mdouchement/Ampeg-Heritage-B-15/Documents/_2011 Heritage HB15.jpg

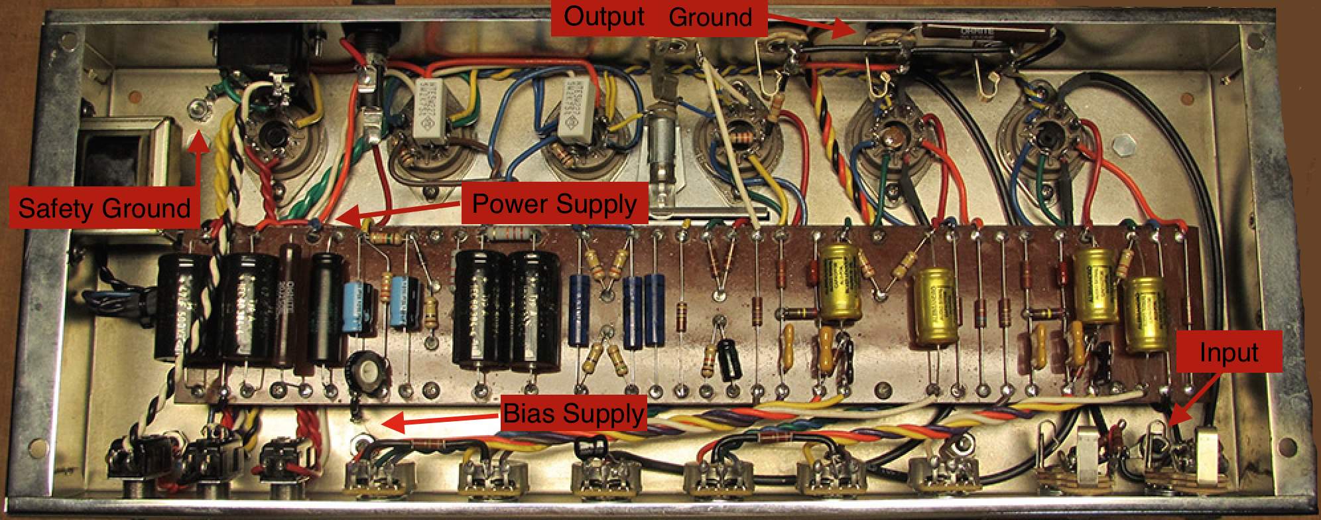
Documents/_2011 Heritage HB15.jpg
