mdouchement/Ampeg-Heritage-B-15/Measures/1964.mods.png

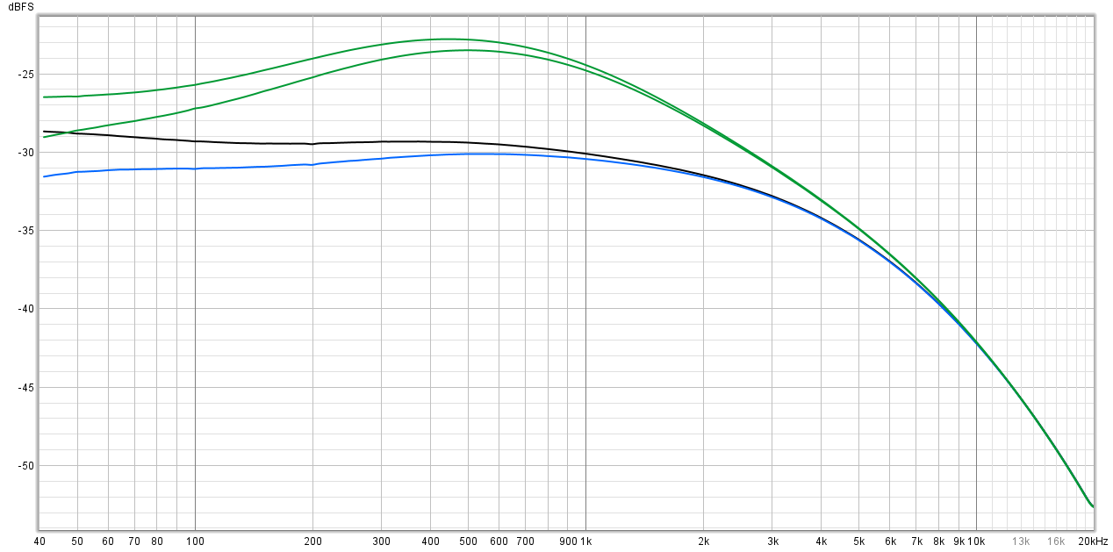
Measures/1964.mods.png
