mdouchement/Ampeg-Heritage-B-15/Measures/1964.tonestack.png

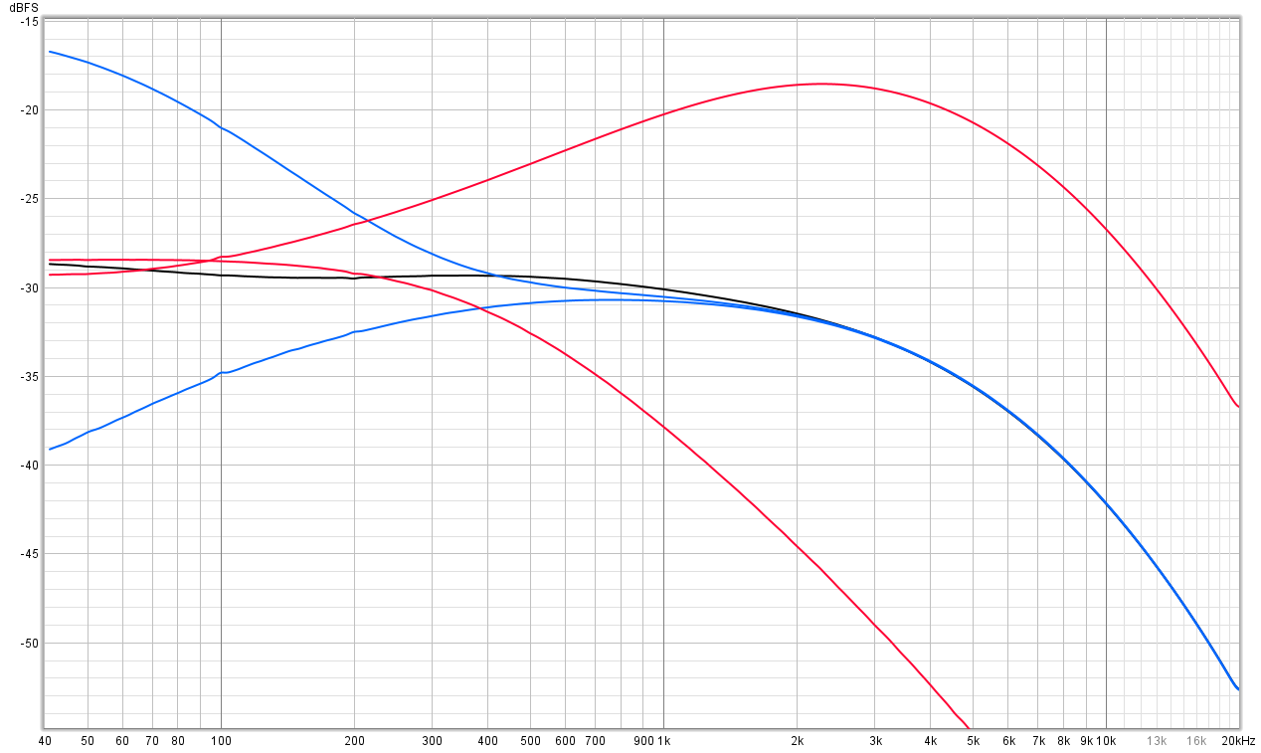
Measures/1964.tonestack.png
