mdouchement/Ampeg-Heritage-B-15/Measures/1966.mods.png

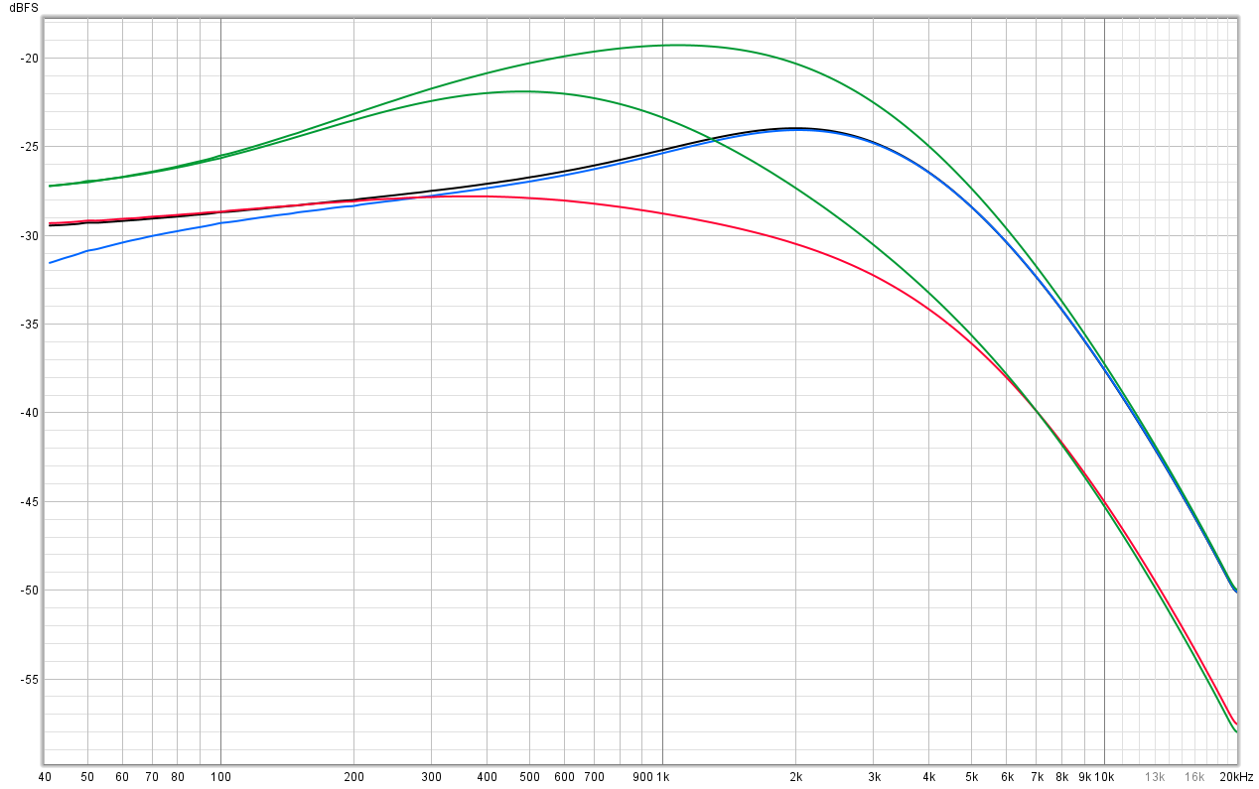
Measures/1966.mods.png
