mdouchement/Ampeg-Heritage-B-15/Measures/1966.tonestack.png

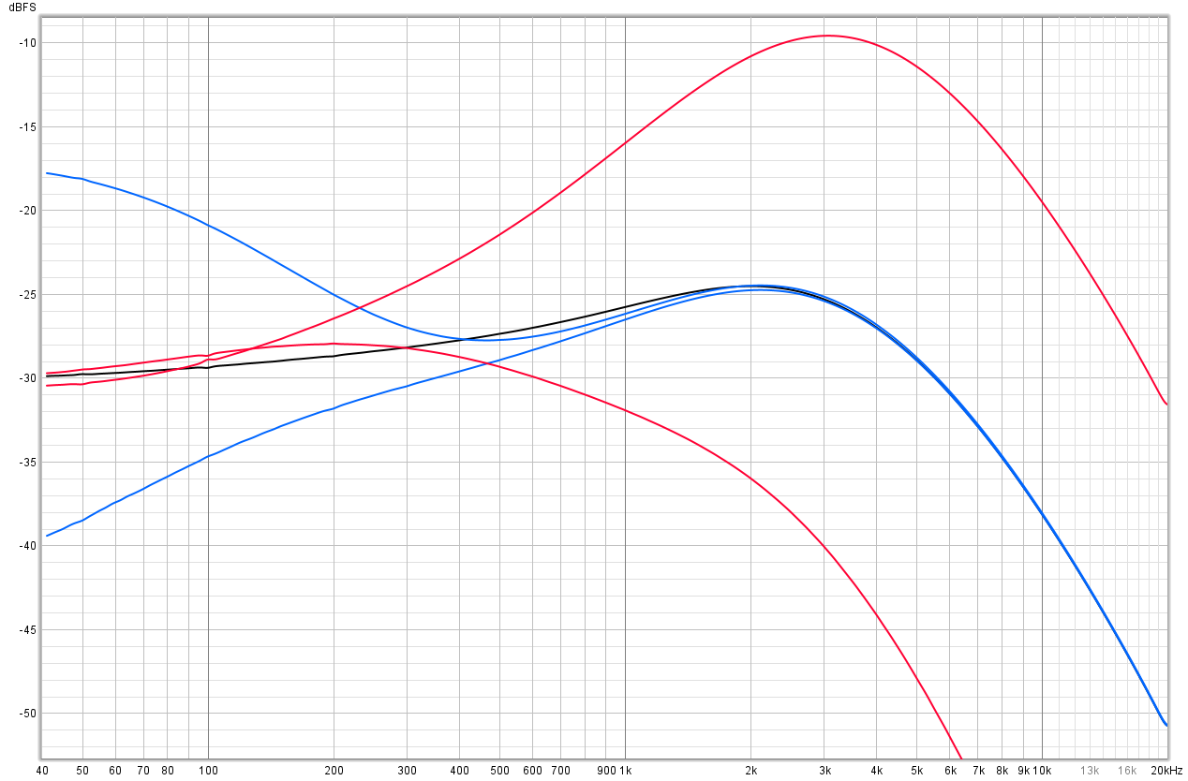
Measures/1966.tonestack.png
